telzo2000/cool836qalble2/img/img00005.jpg

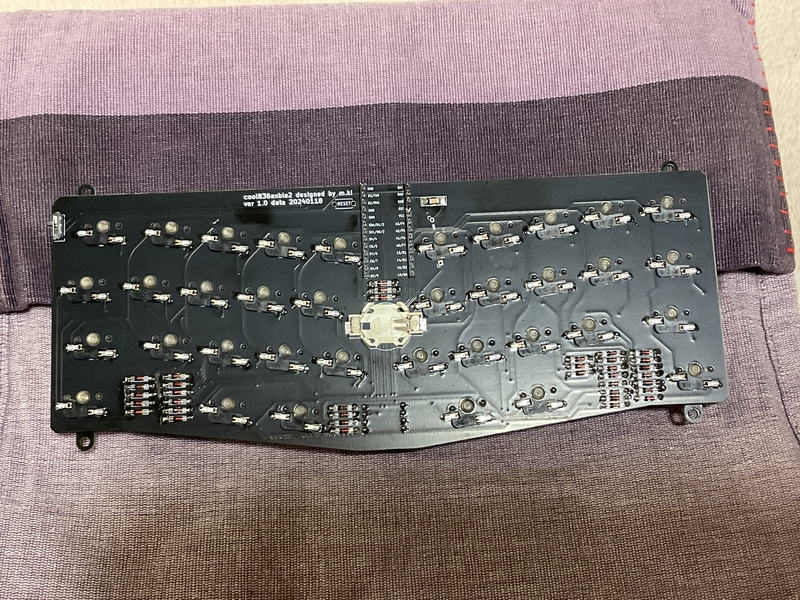
img/img00005.jpg
