telzo2000/cool836qalble2/img/img00006.jpg

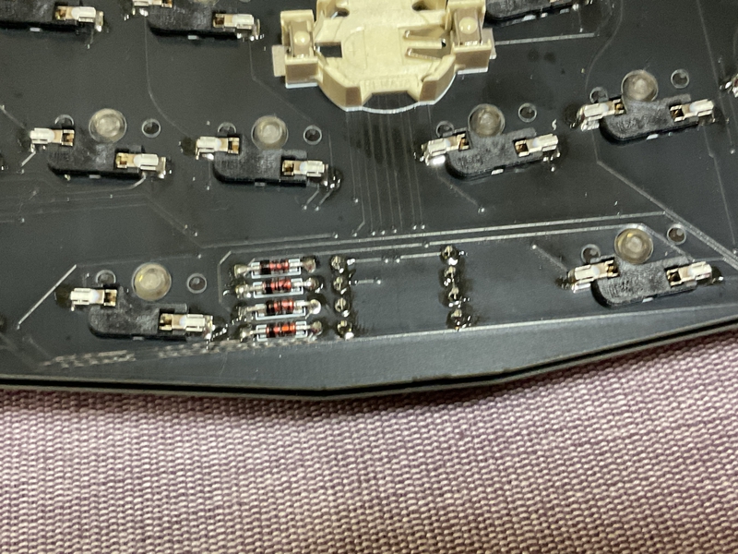
img/img00006.jpg
